opm-martinos/opm_coils/hardware/By_coil/By_coil_notes/By_coil.jpg

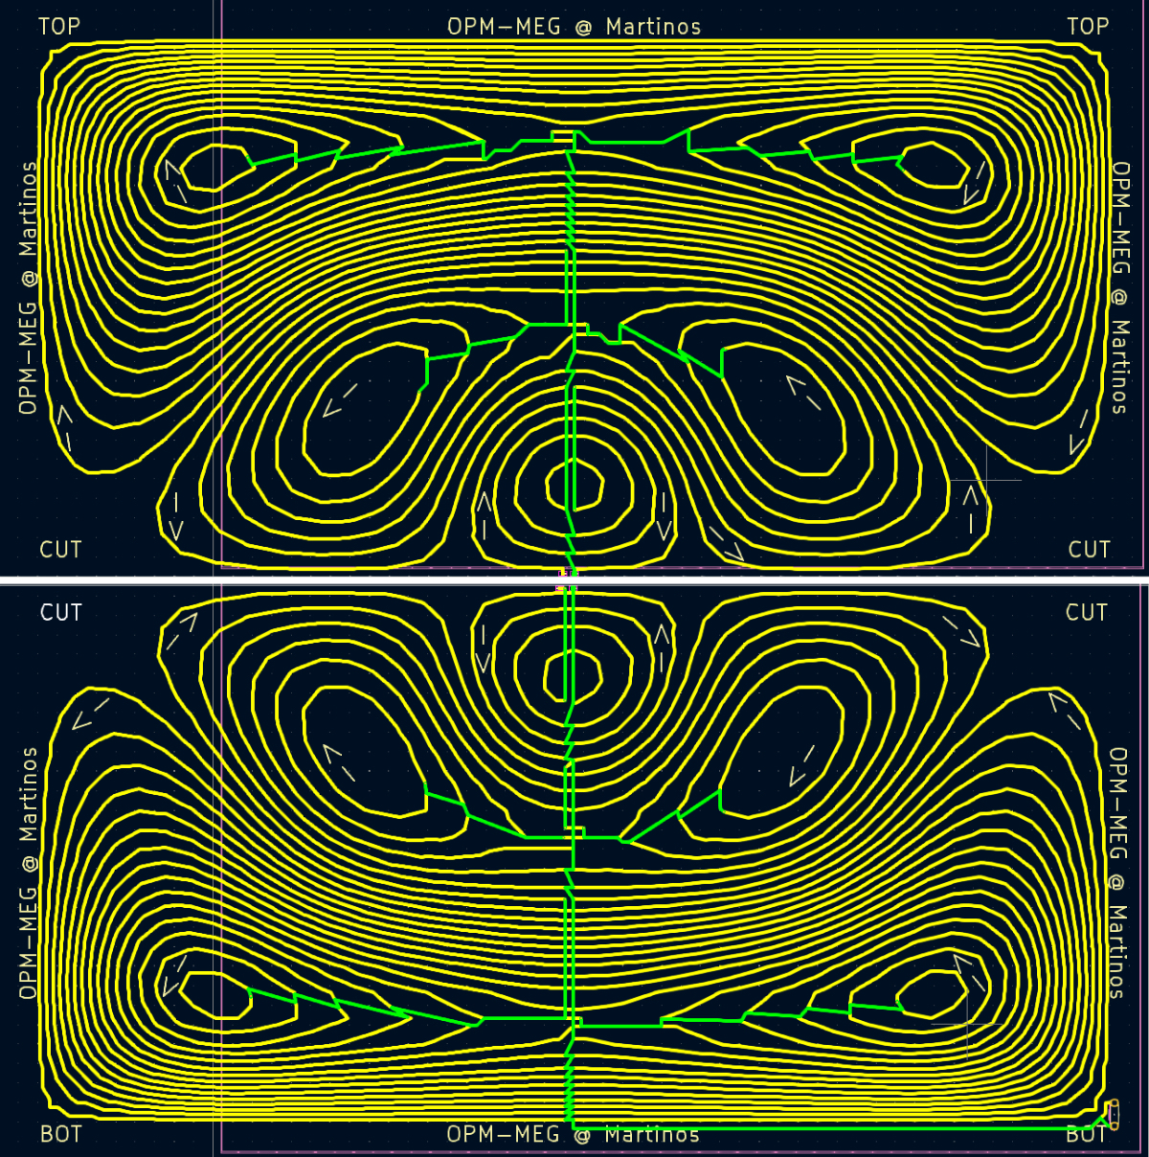
hardware/By_coil/By_coil_notes/By_coil.jpg
