opm-martinos/opm_coils/hardware/By_coil/By_coil_notes/cuts.png

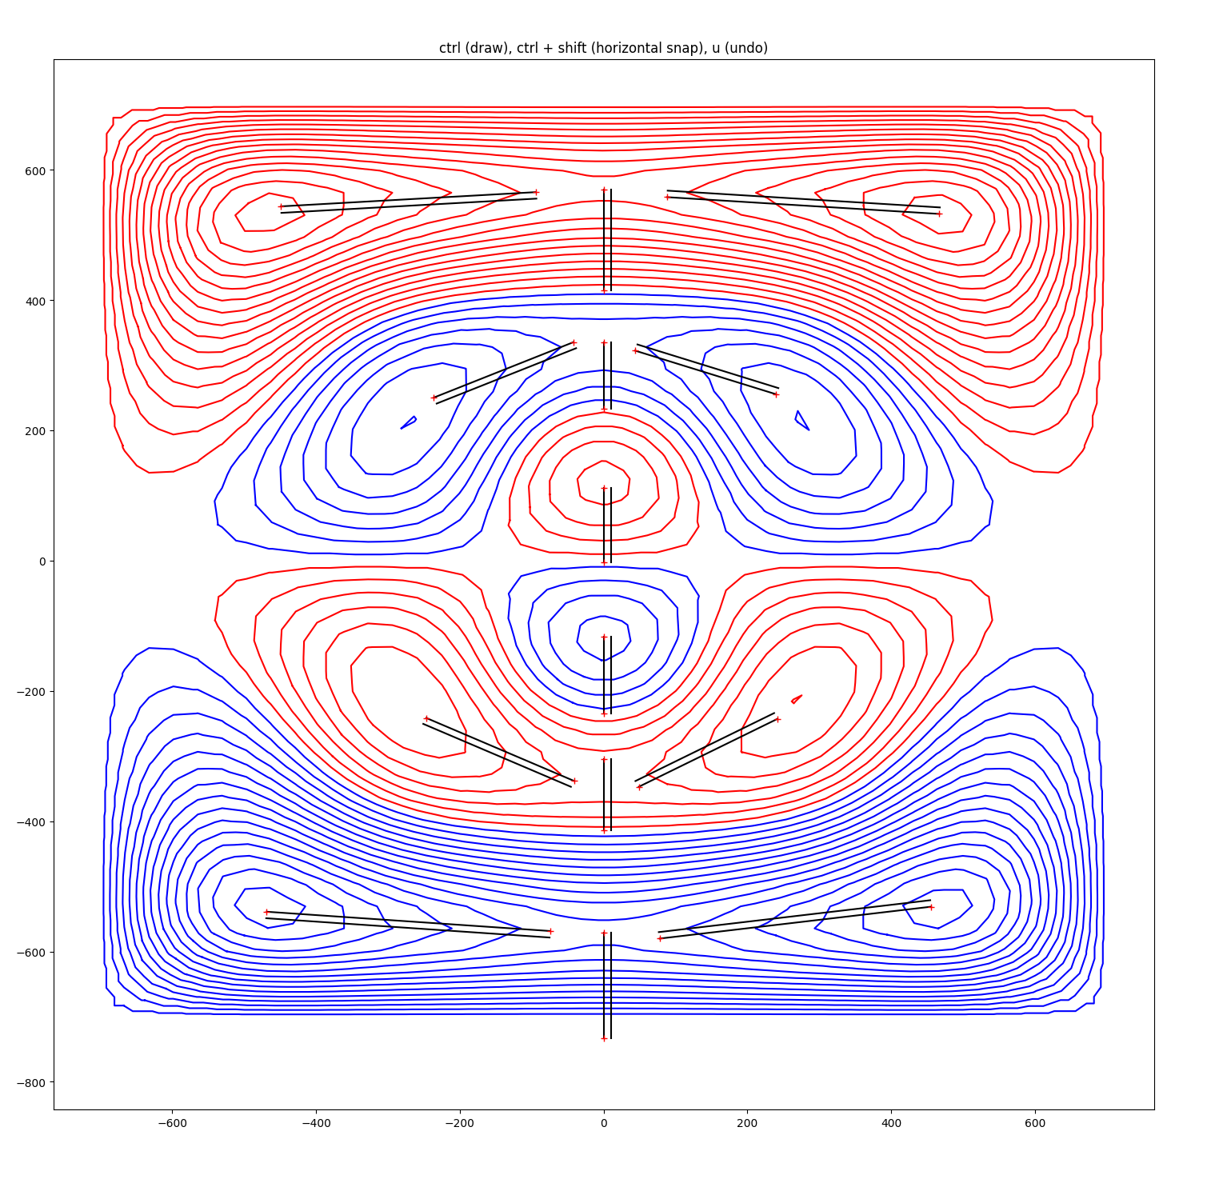
hardware/By_coil/By_coil_notes/cuts.png
