opm-martinos/opm_coils/hardware/By_coil/By_coil_notes/terminal_spacing_2.png

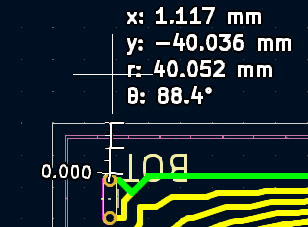
hardware/By_coil/By_coil_notes/terminal_spacing_2.png
