opm-martinos/opm_coils/hardware/By_coil/By_coil_notes/top.png

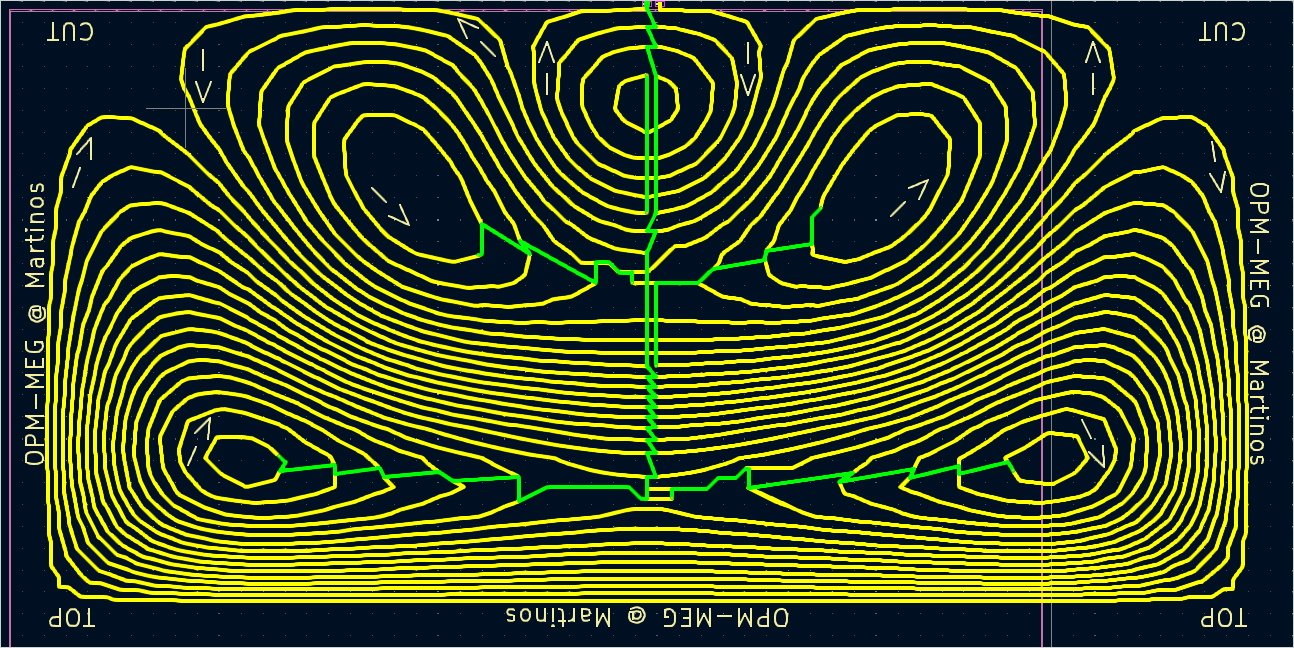
hardware/By_coil/By_coil_notes/top.png
