opm-martinos/opm_coils/hardware/notes/Brookes_params.png

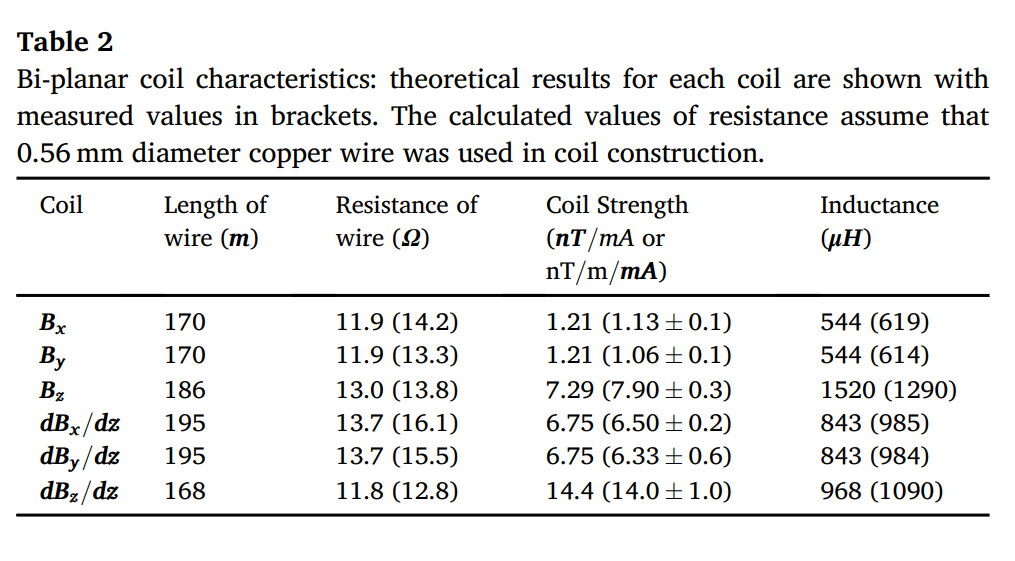
hardware/notes/Brookes_params.png
