opm-martinos/opm_coils/hardware/notes/Bx_1st.png

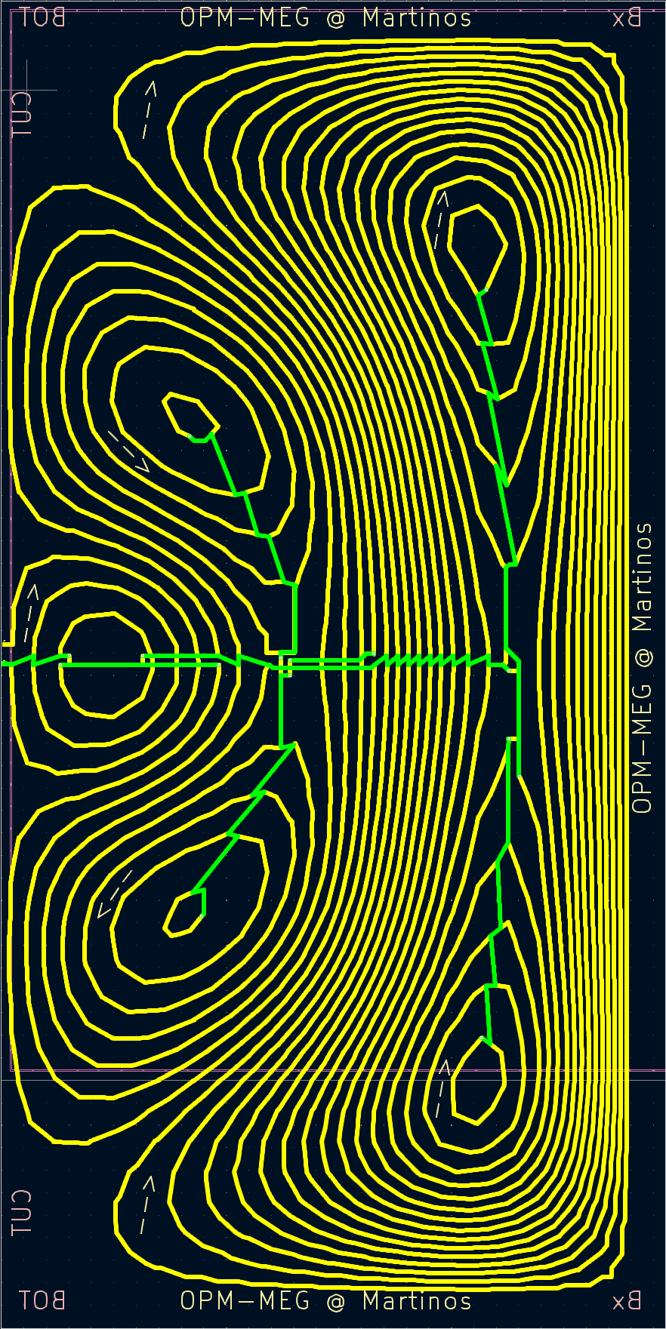
hardware/notes/Bx_1st.png
