opm-martinos/opm_coils/hardware/notes/Bx_2nd.png

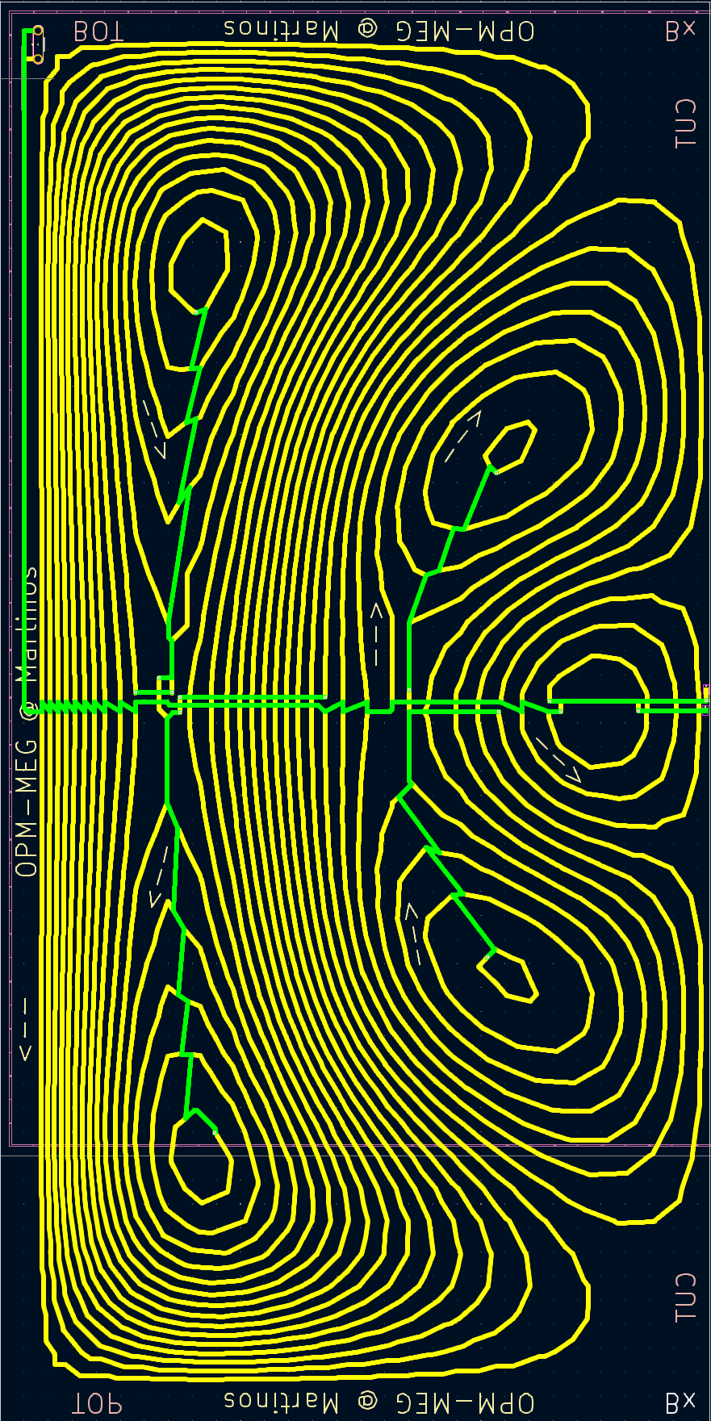
hardware/notes/Bx_2nd.png
