opm-martinos/opm_coils/hardware/notes/Bx_cuts2.png

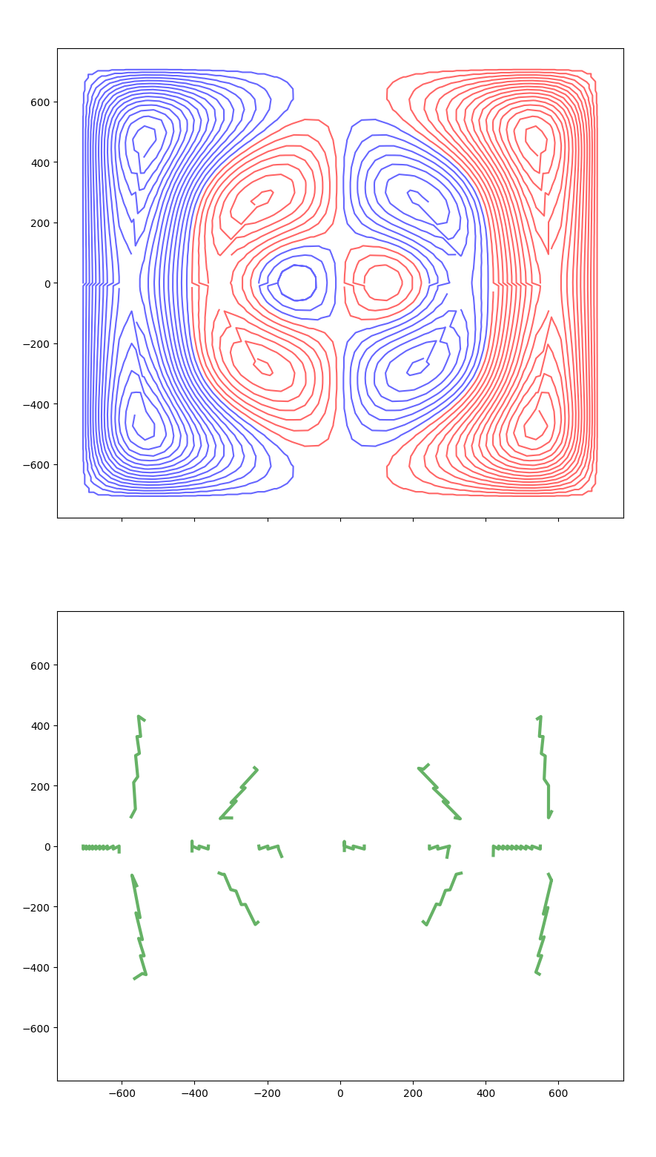
hardware/notes/Bx_cuts2.png
