opm-martinos/opm_coils/hardware/notes/Bx_cuts.png

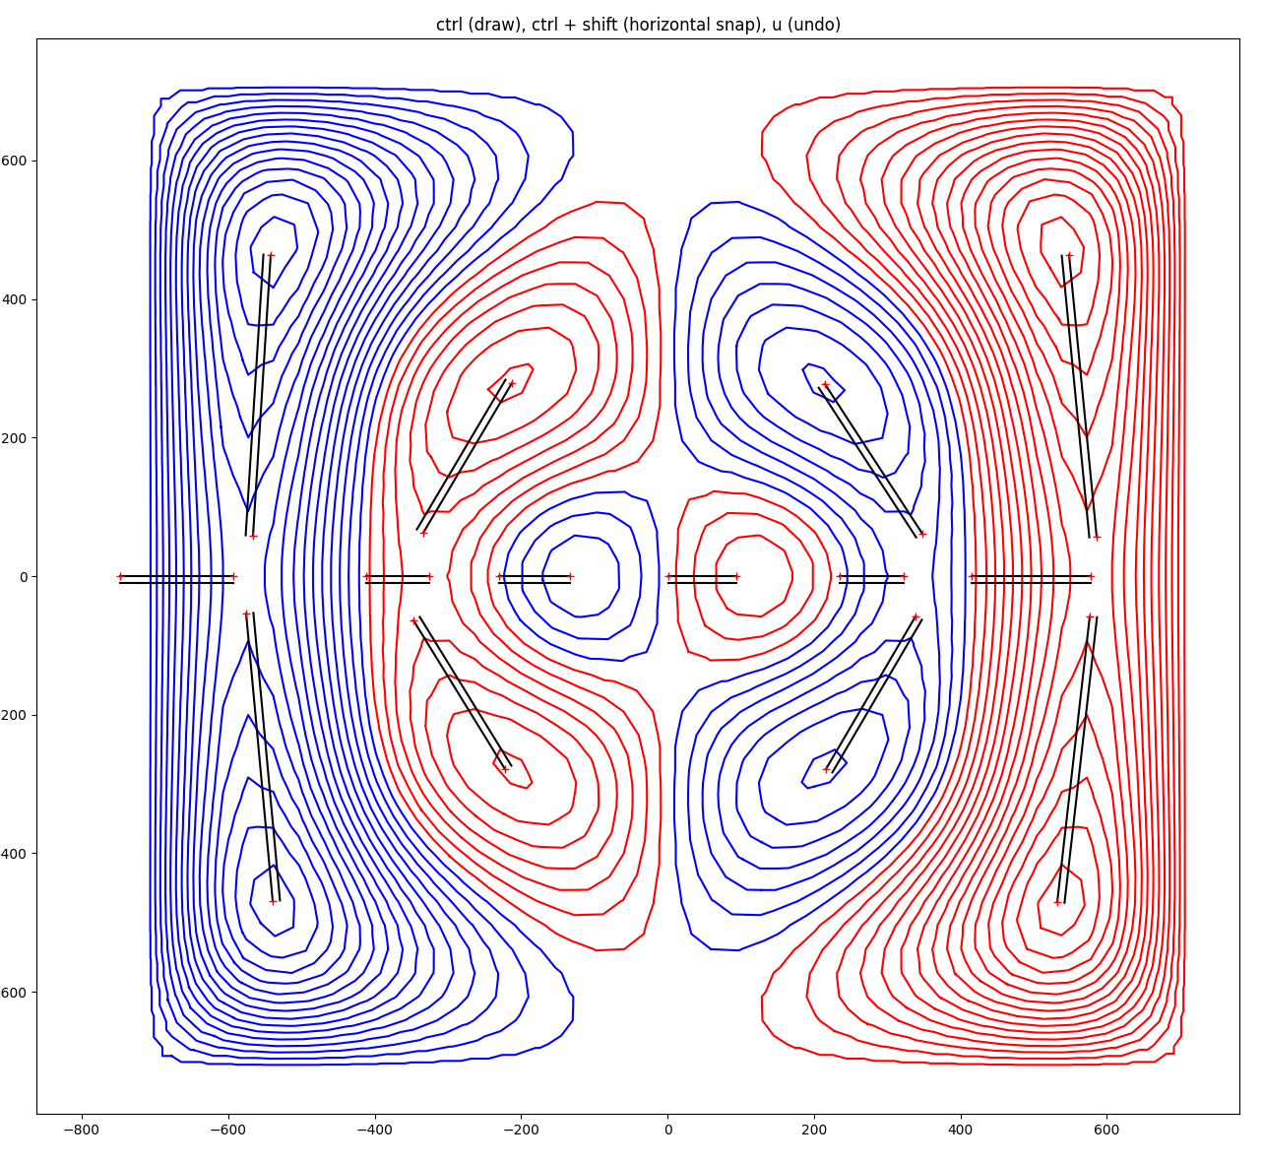
hardware/notes/Bx_cuts.png
