opm-martinos/opm_coils/hardware/notes/Bz.png

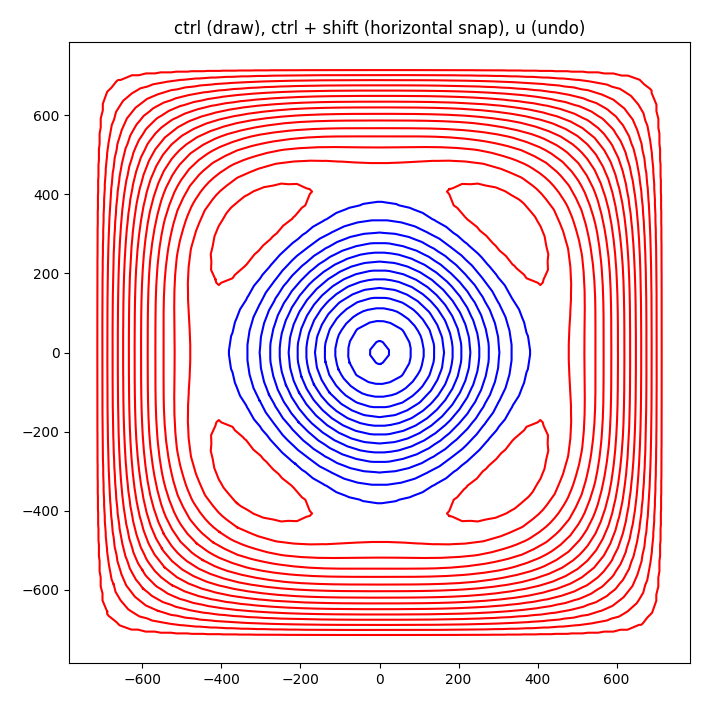
hardware/notes/Bz.png
