opm-martinos/opm_coils/hardware/notes/Bz_1st.png

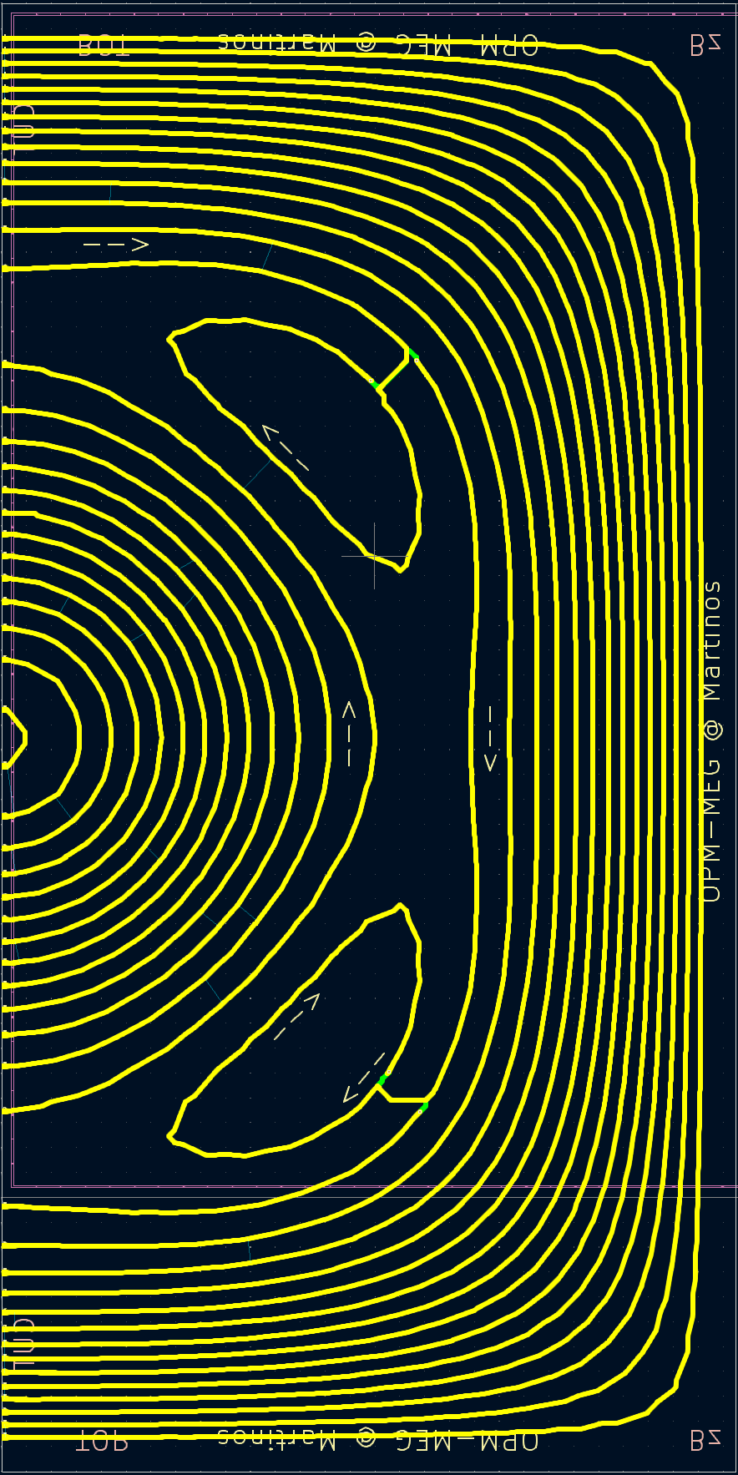
hardware/notes/Bz_1st.png
