opm-martinos/opm_coils/hardware/notes/Bz_2nd.png

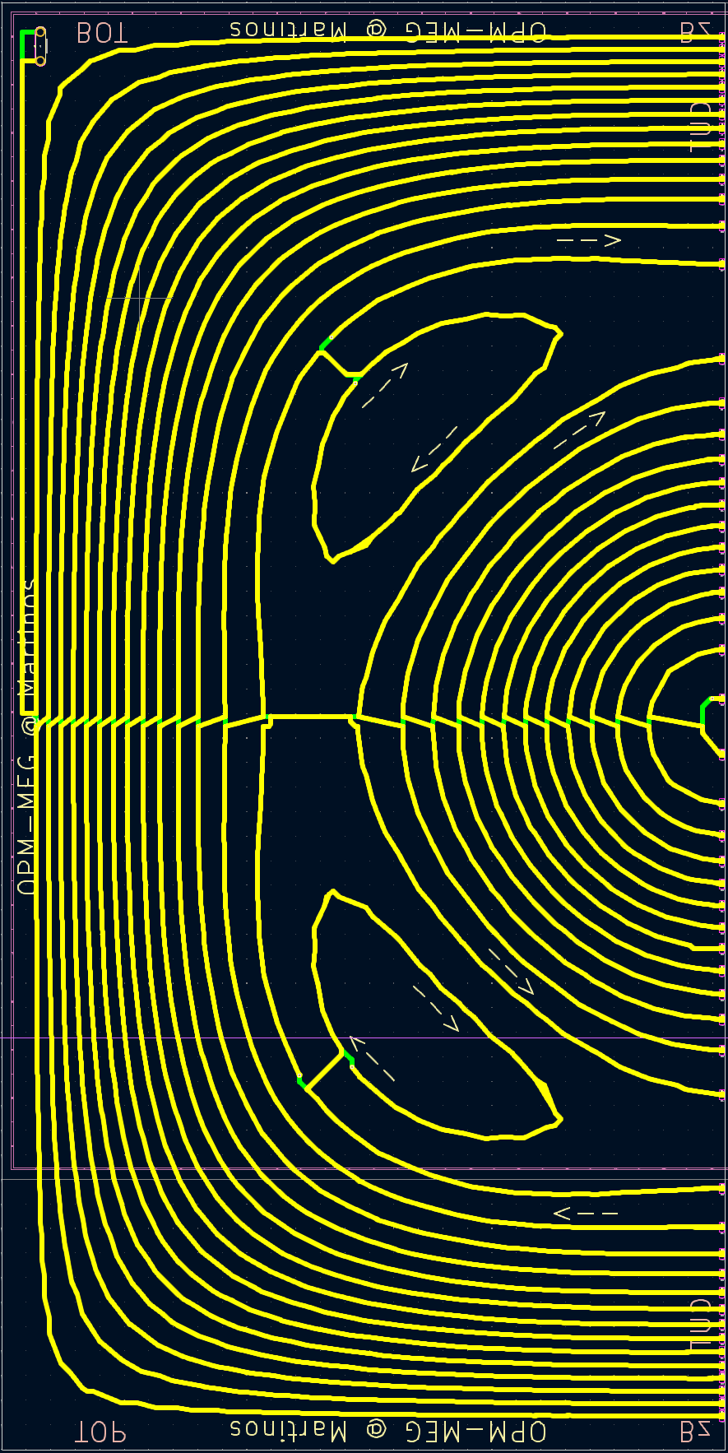
hardware/notes/Bz_2nd.png
