opm-martinos/opm_coils/hardware/notes/Bz_cuts2.png

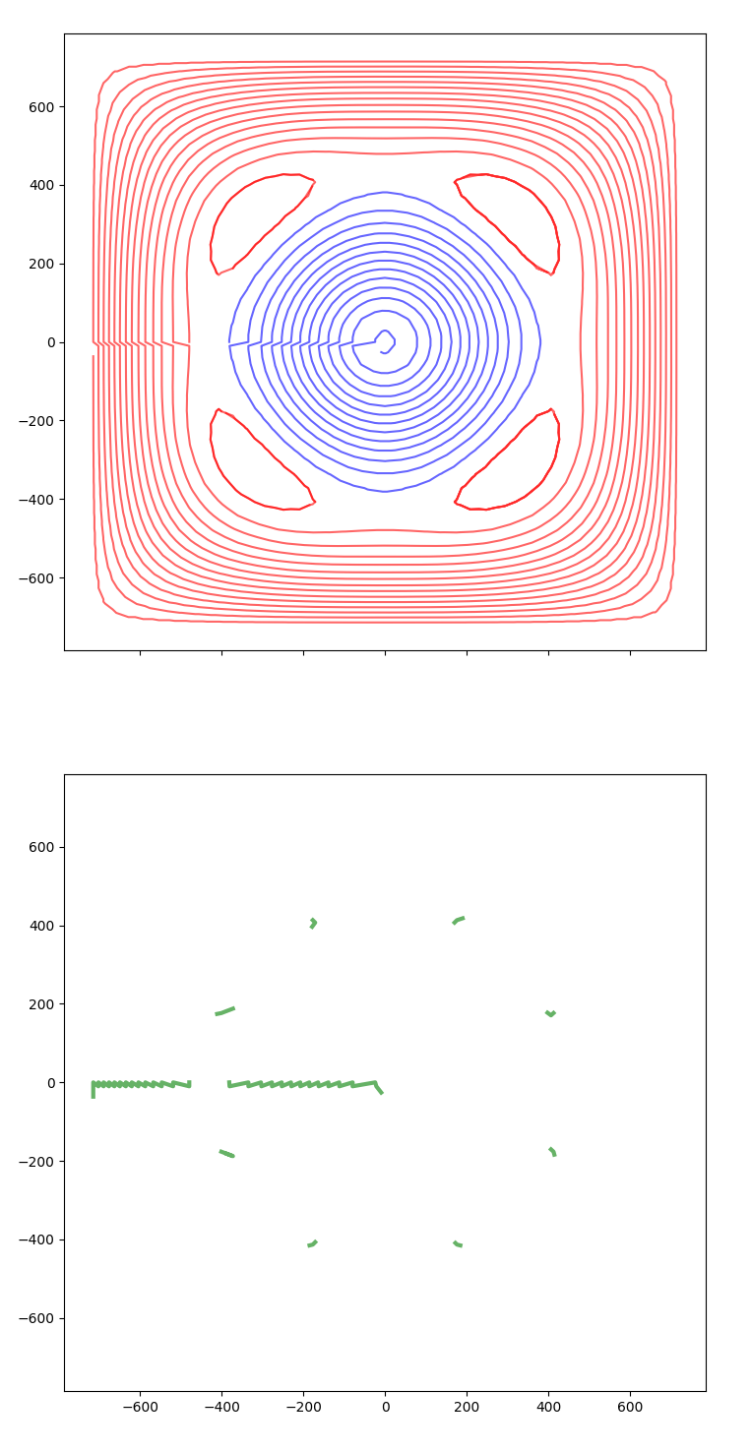
hardware/notes/Bz_cuts2.png
