opm-martinos/opm_coils/hardware/notes/Bz_cuts.png

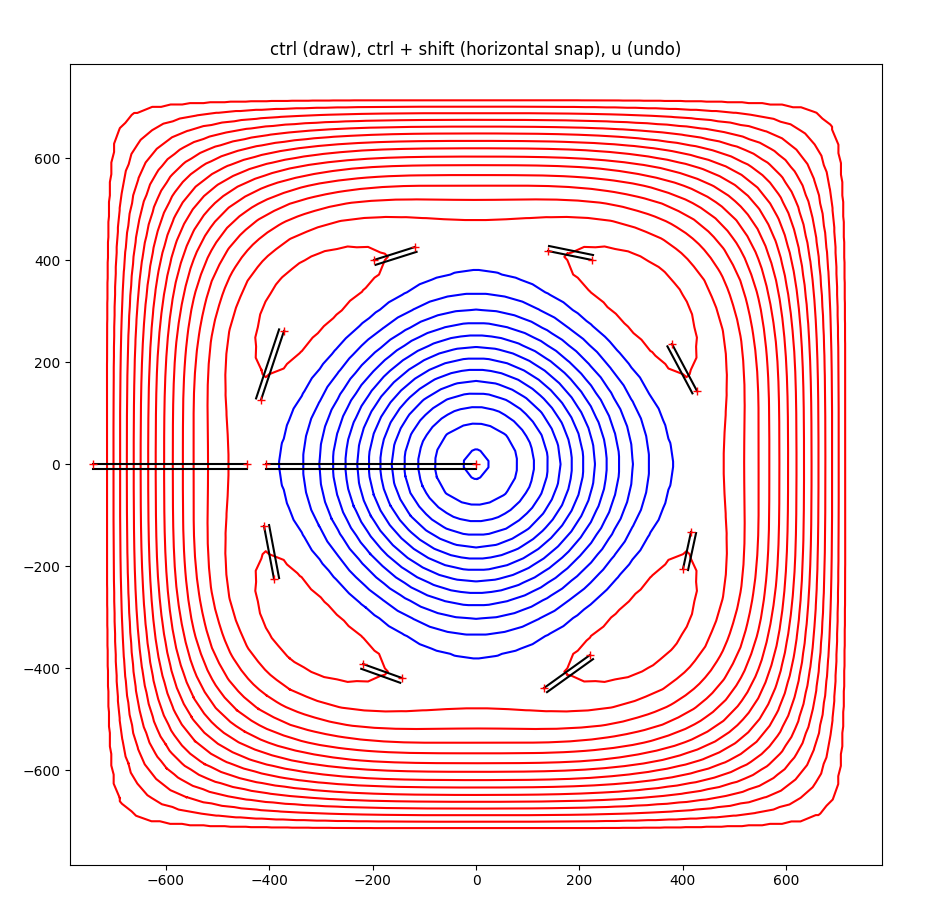
hardware/notes/Bz_cuts.png
