opm-martinos/opm_coils/hardware/notes/Gx.png

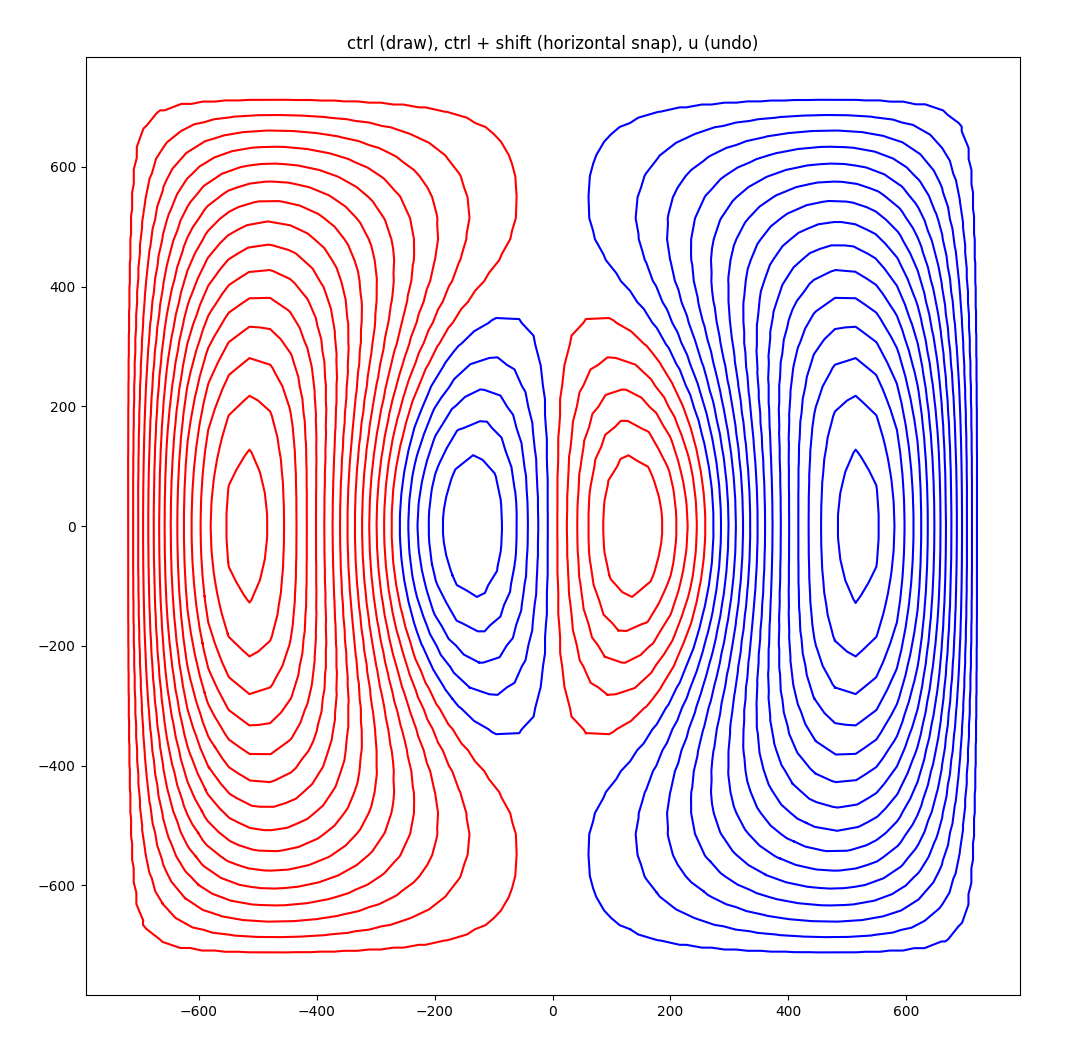
hardware/notes/Gx.png
