opm-martinos/opm_coils/hardware/notes/Gx_2nd.png

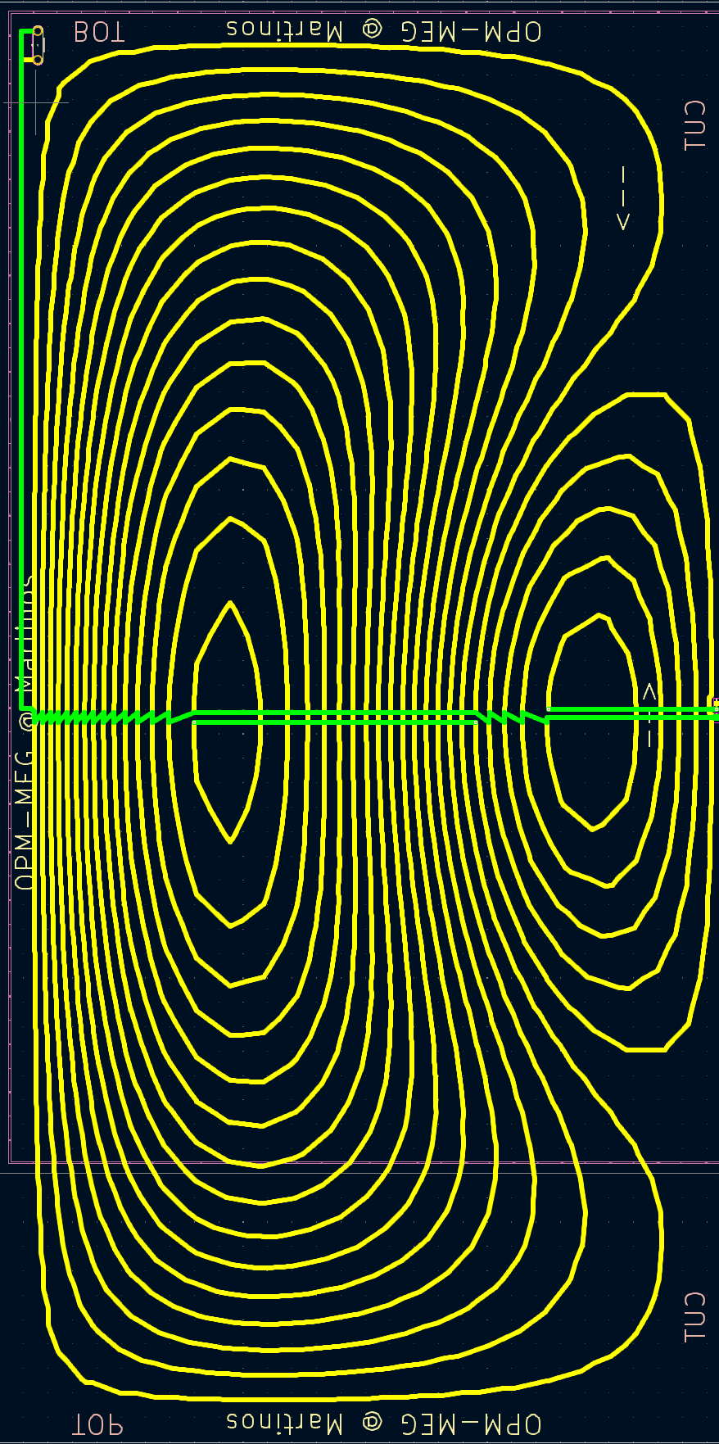
hardware/notes/Gx_2nd.png
