opm-martinos/opm_coils/hardware/notes/Gx_cuts2.png

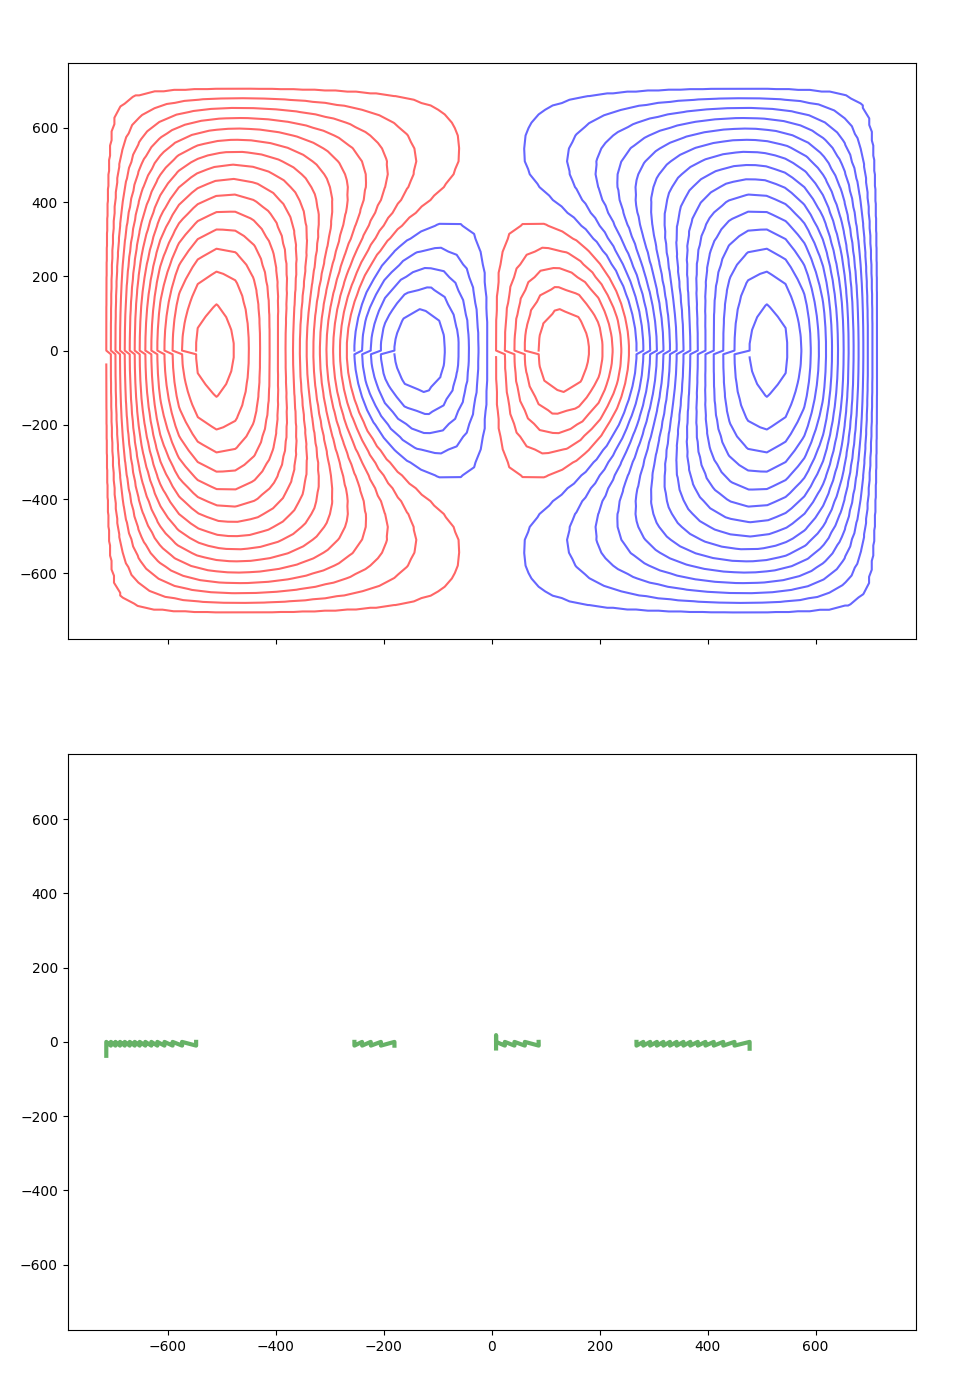
hardware/notes/Gx_cuts2.png
