opm-martinos/opm_coils/hardware/notes/Gy.png

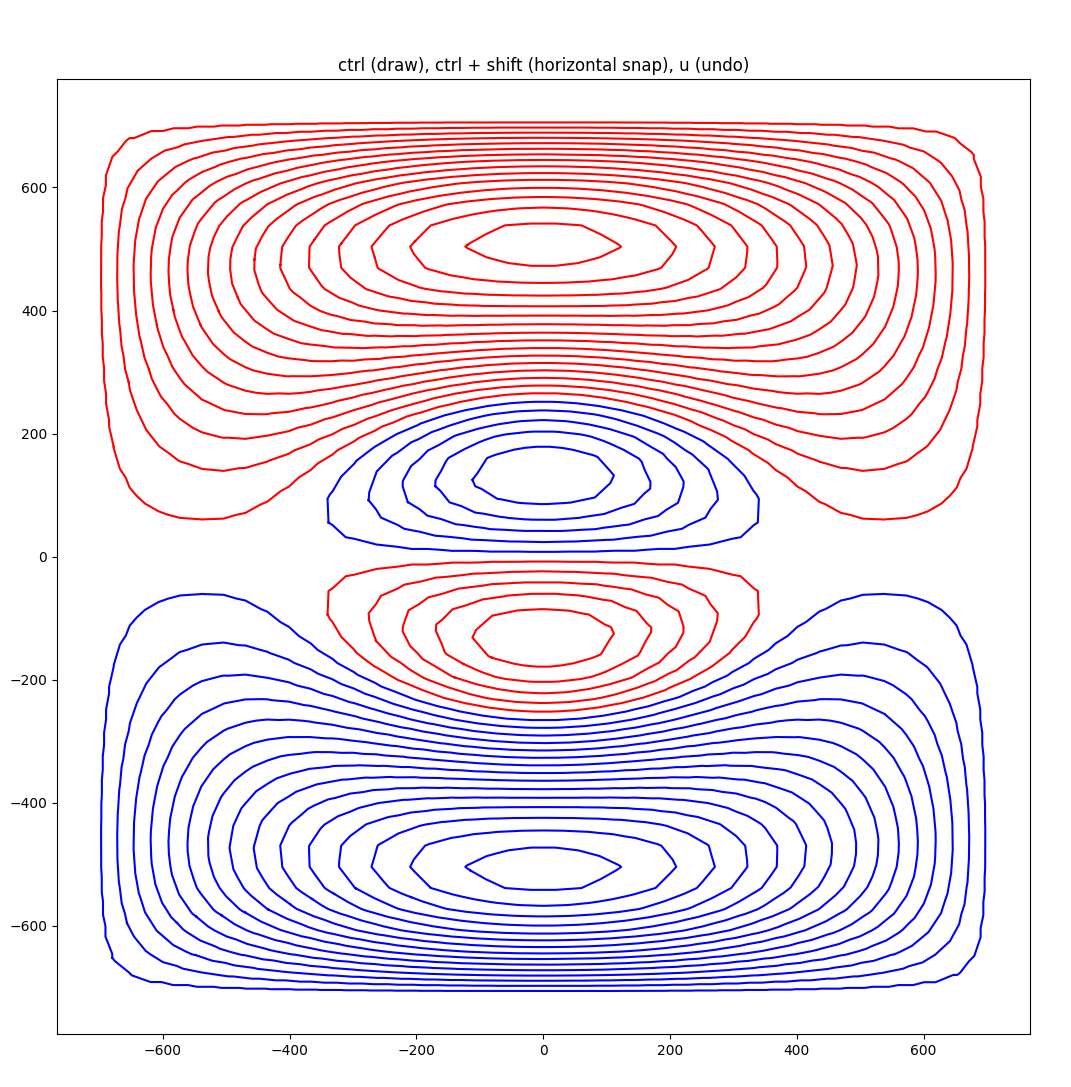
hardware/notes/Gy.png
