opm-martinos/opm_coils/hardware/notes/Gy_1st.png

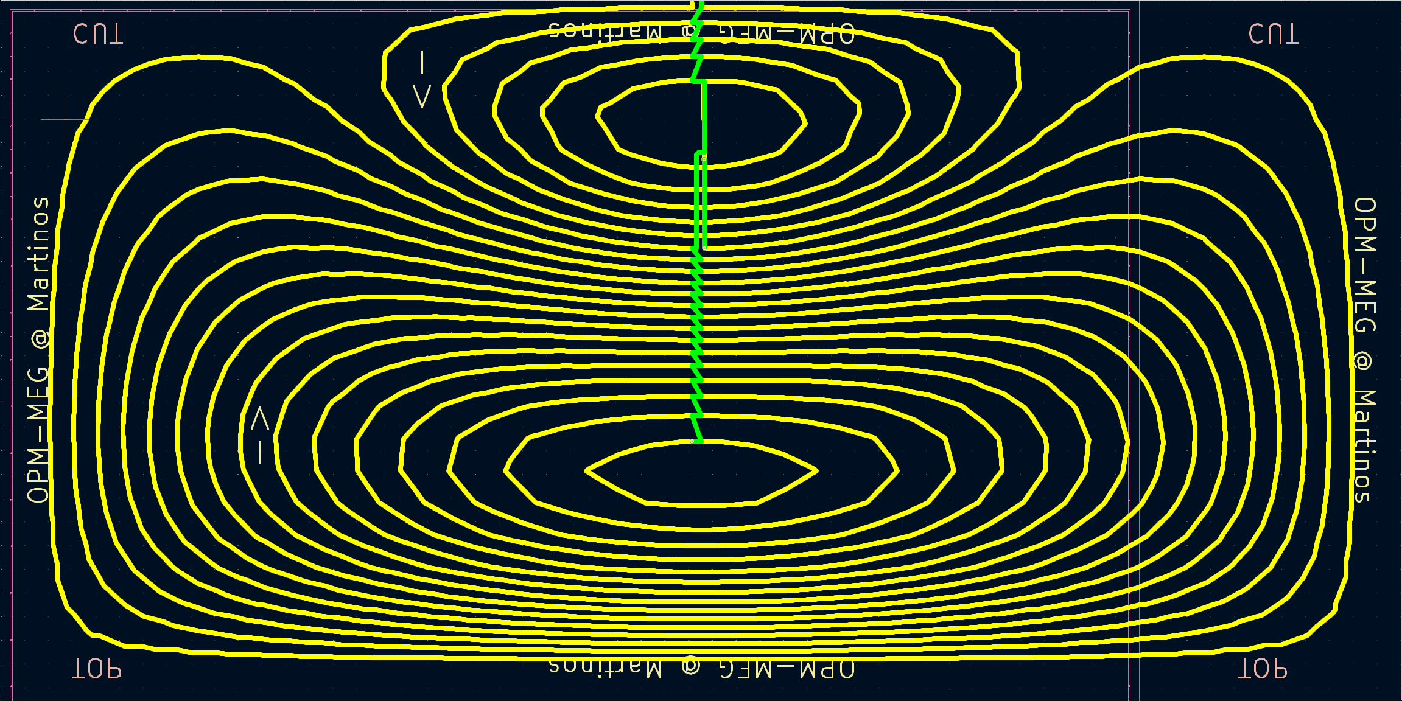
hardware/notes/Gy_1st.png
