opm-martinos/opm_coils/hardware/notes/Gy_2nd.png

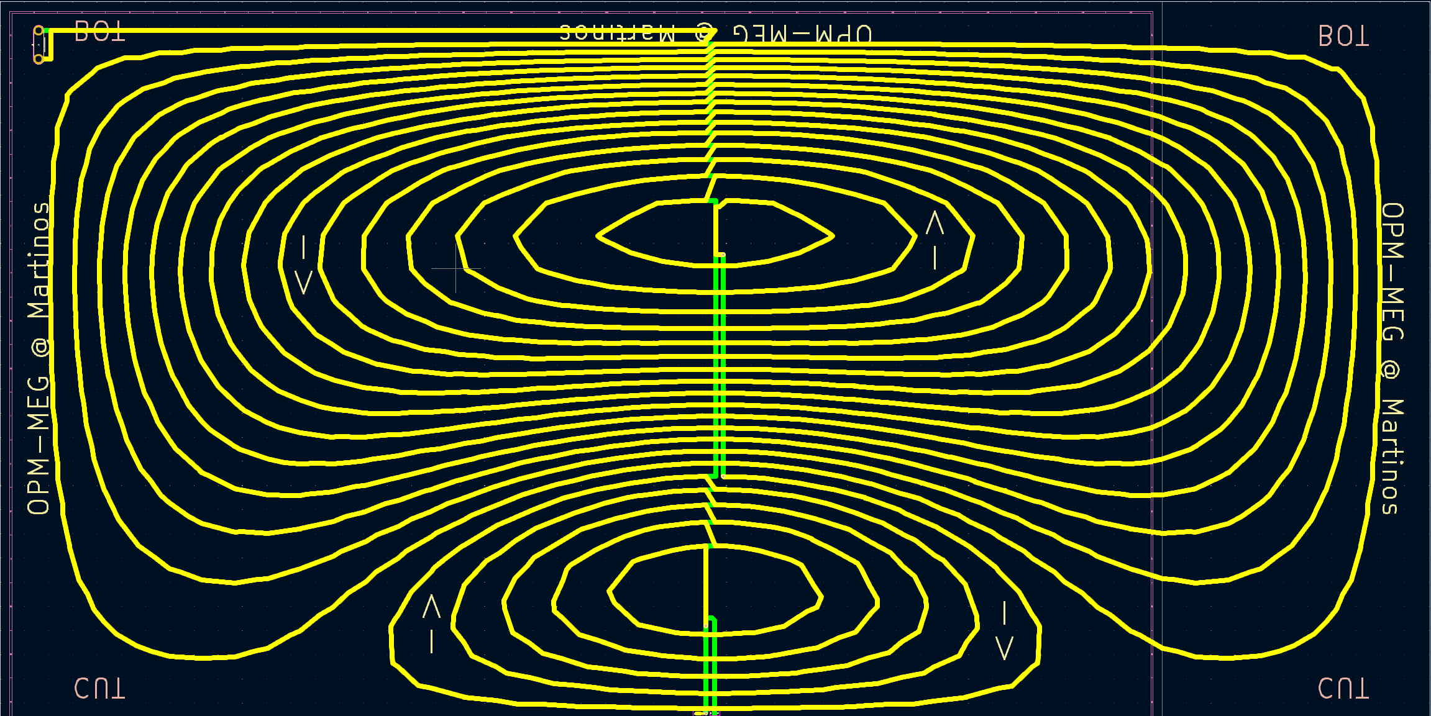
hardware/notes/Gy_2nd.png
