opm-martinos/opm_coils/hardware/notes/Gy_cuts2.png

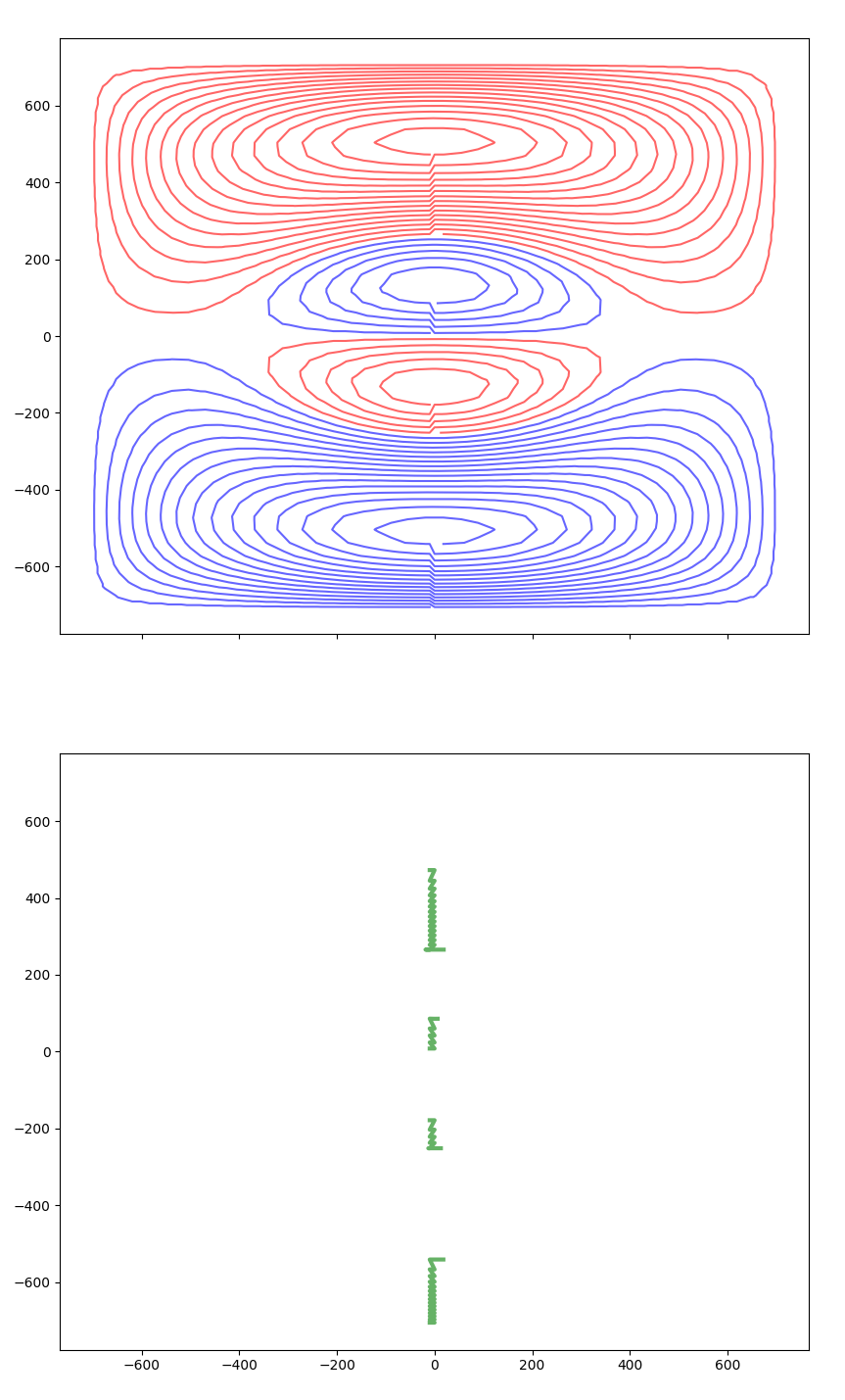
hardware/notes/Gy_cuts2.png
