opm-martinos/opm_coils/hardware/notes/Gz.png

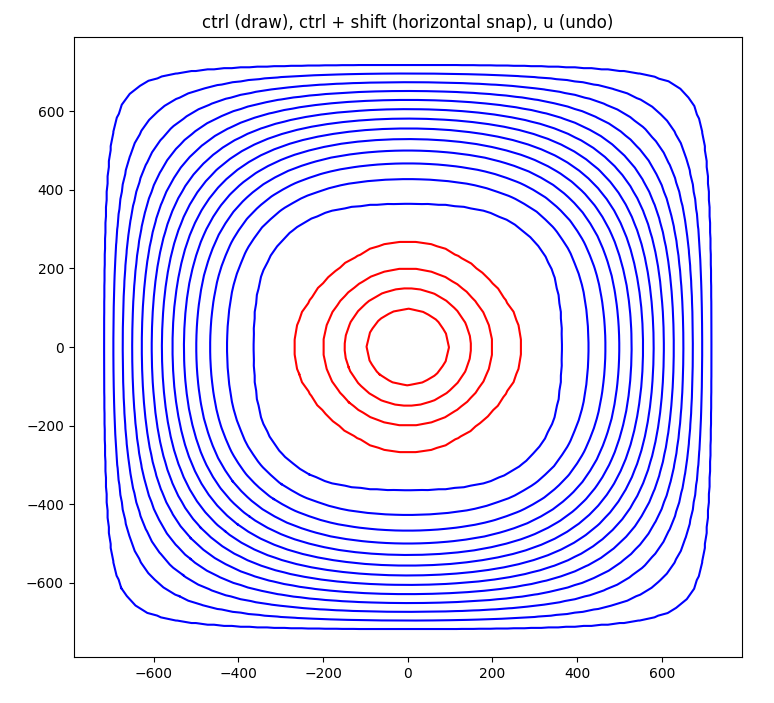
hardware/notes/Gz.png
