opm-martinos/opm_coils/hardware/notes/Gz_1st.png

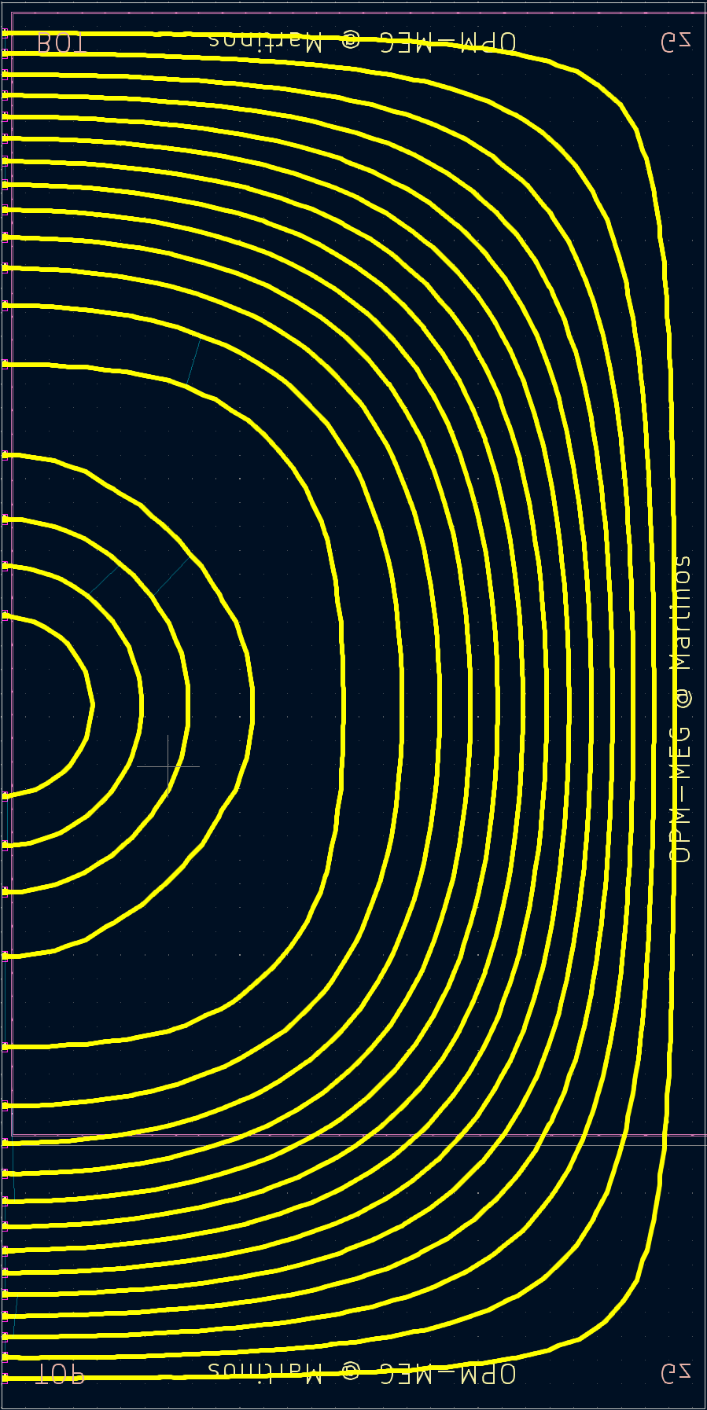
hardware/notes/Gz_1st.png
