opm-martinos/opm_coils/hardware/notes/Gz_2nd.png

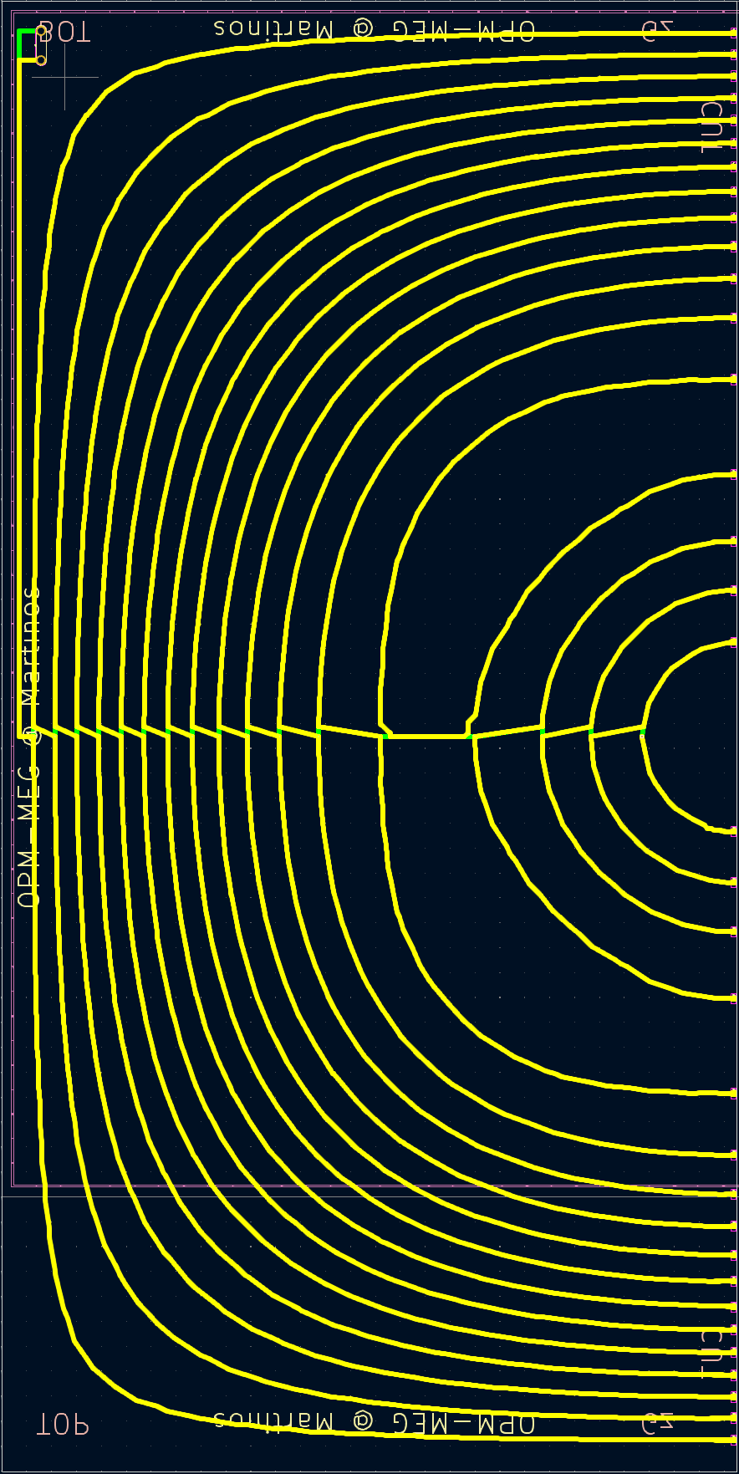
hardware/notes/Gz_2nd.png
