opm-martinos/opm_coils/hardware/notes/Gz_cuts2.png

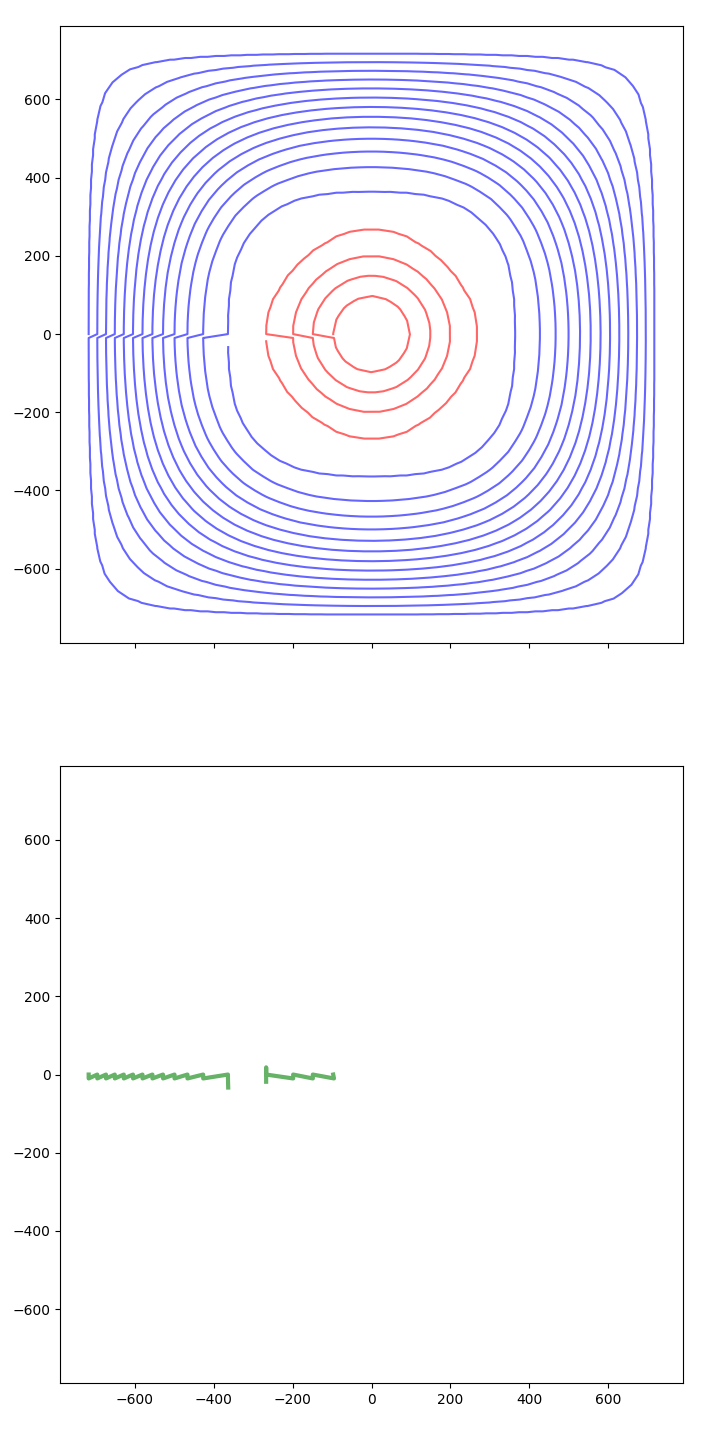
hardware/notes/Gz_cuts2.png
