opm-martinos/opm_coils/hardware/notes/Gz_cuts.png

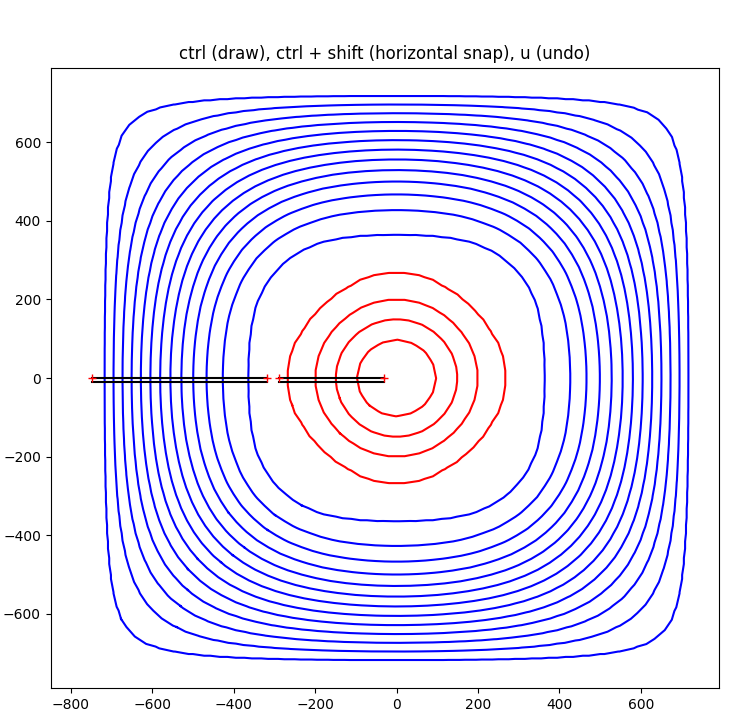
hardware/notes/Gz_cuts.png
