opm-martinos/opm_coils/hardware/Bx_coil/second/coil_template_second.kicad_sch

## KiCad design hardware/Bx_coil/second/coil_template_second.kicad_sch (2025-02-18)

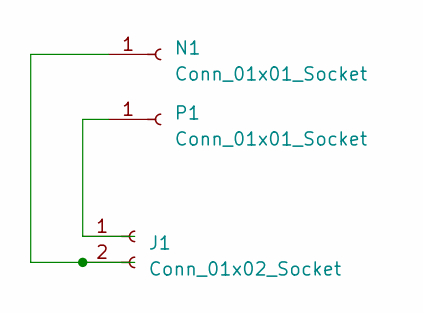
[picture p40: schematic coil_template_second.kicad_sch]

Parts:
J1: Conn_01x02_Socket; Banana_Jack_2Pin_Vert
N1: Conn_01x01_Socket; SolderWirePad_1x01_SMD_5x10mm_custom
P1: Conn_01x01_Socket; SolderWirePad_1x01_SMD_5x10mm_custom

Connections:
unnamed: J1.1, P1.1
unnamed: J1.2, N1.1
