opm-martinos/opm_coils/hardware/By_coil/top/coil_template_top.kicad_sch

## KiCad design hardware/By_coil/top/coil_template_top.kicad_sch (2025-02-18)

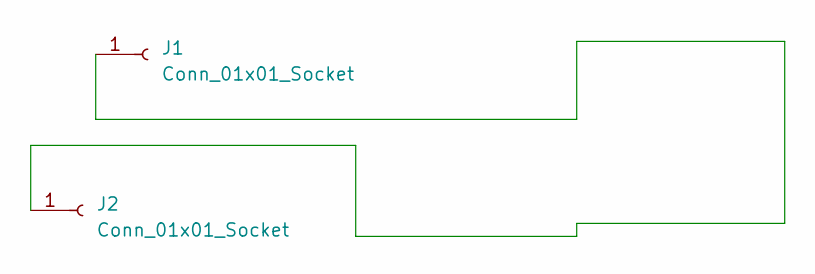
[picture p41: schematic coil_template_top.kicad_sch]

Parts:
J1, J2: Conn_01x01_Socket; SolderWirePad_1x01_SMD_5x10mm_custom

Connections:
unnamed: J1.1, J2.1
